planliu/HeadScanner/Solidworks_Files/SCANNER_outerarm_end.SLDPRT

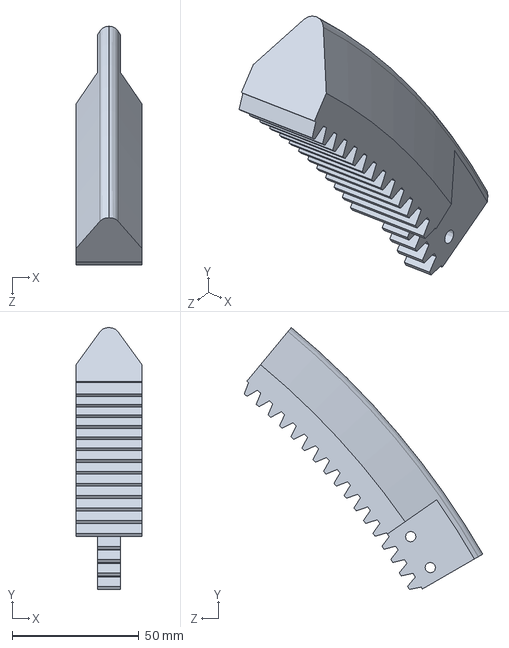
[picture p22: CAD file, 2024-10-23]
Solidworks_Files/SCANNER_outerarm_end.SLDPRT
26.0 x 103.2 x 94.0 mm
