planliu/HeadScanner/Solidworks_Files/SCANNER_uppergearlarge.SLDPRT

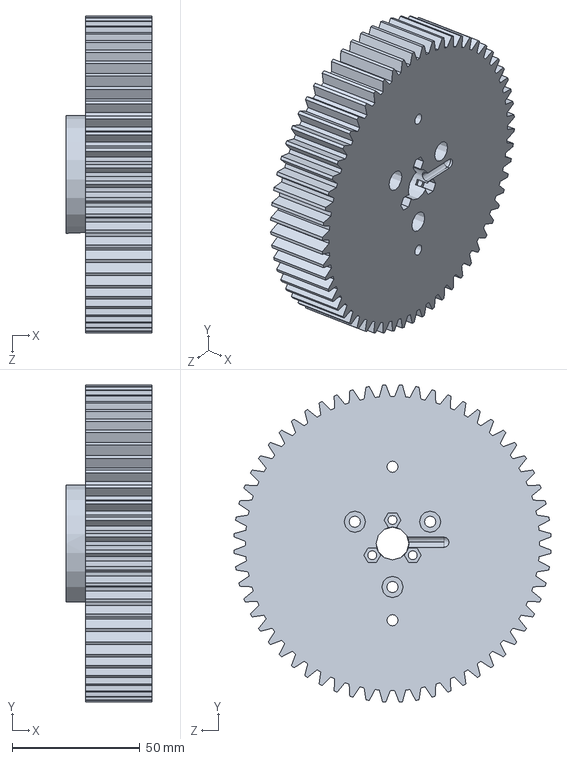
[picture p23: CAD file, 2024-10-23]
Solidworks_Files/SCANNER_uppergearlarge.SLDPRT
33.5 x 123.9 x 123.9 mm
