planliu/HeadScanner/Solidworks_Files/SCANNER_uppergearlargemating.SLDPRT

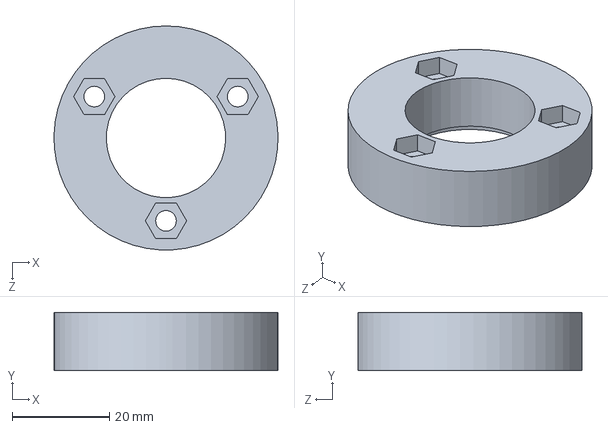
[picture p24: CAD file, 2024-10-23]
Solidworks_Files/SCANNER_uppergearlargemating.SLDPRT
46.0 x 12.0 x 46.0 mm
