planliu/HeadScanner/Solidworks_Files/SCANNER_shaft.SLDPRT

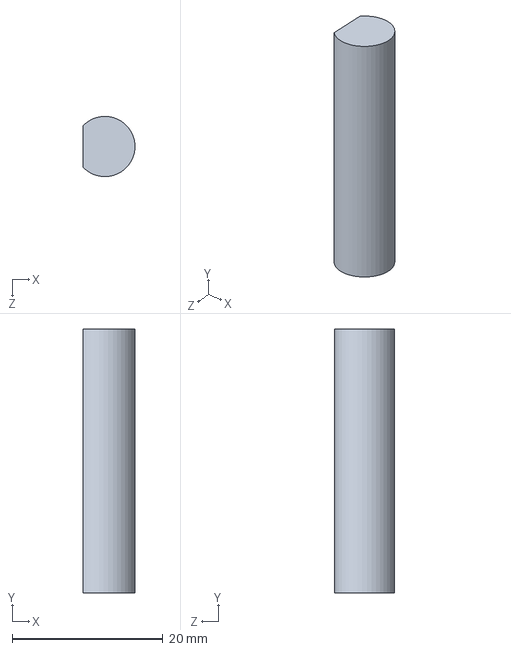
[picture p25: CAD file, 2024-10-23]
Solidworks_Files/SCANNER_shaft.SLDPRT
6.89 x 35.0 x 7.99 mm
