planliu/HeadScanner/Solidworks_Files/SCANNER_bodymidR.SLDPRT

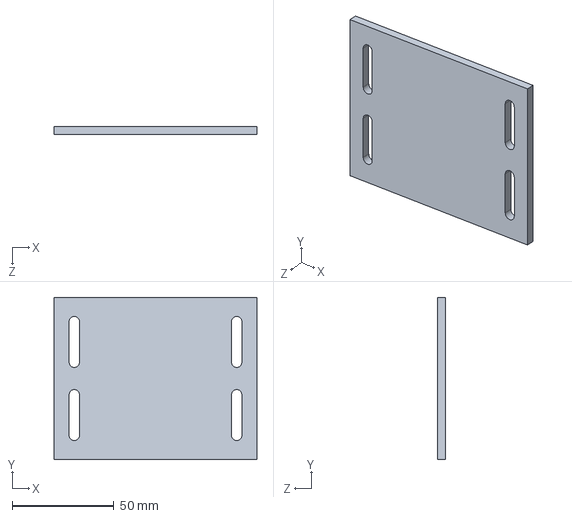
[picture p26: CAD file, 2024-10-23]
Solidworks_Files/SCANNER_bodymidR.SLDPRT
100.0 x 80.0 x 4.00 mm
