planliu/HeadScanner/Solidworks_Files/SCANNER_bodymidR2.SLDPRT

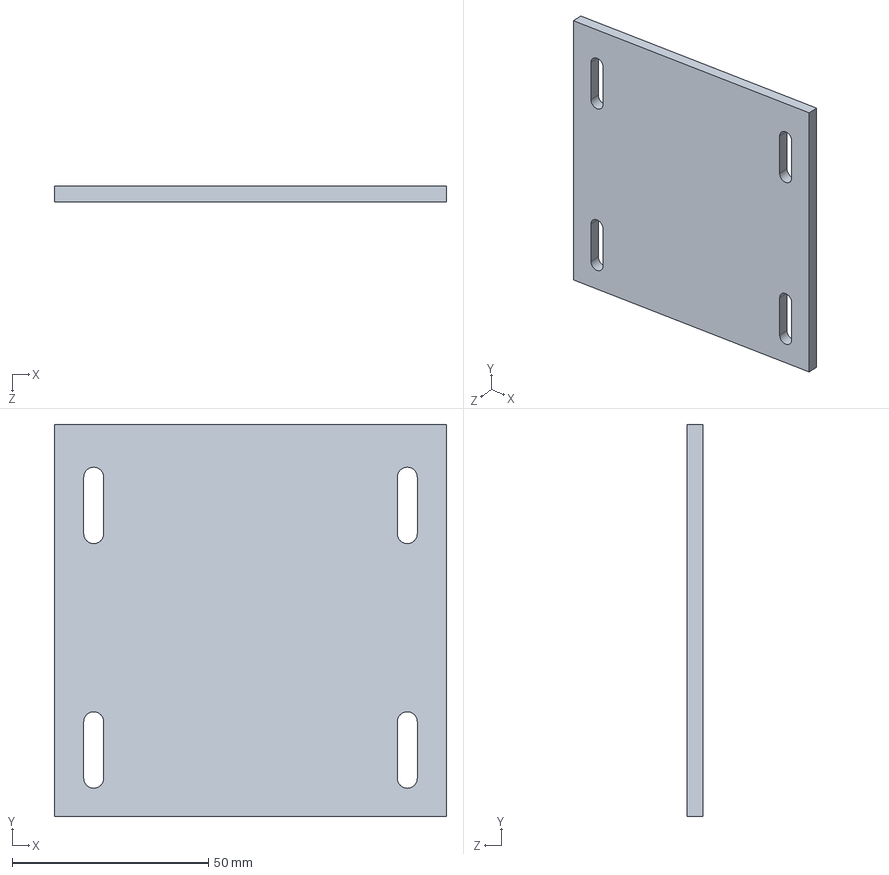
[picture p27: CAD file, 2024-10-23]
Solidworks_Files/SCANNER_bodymidR2.SLDPRT
100.0 x 100.0 x 4.00 mm
