planliu/HeadScanner/Solidworks_Files/SCANNER_innerarm_end.SLDPRT

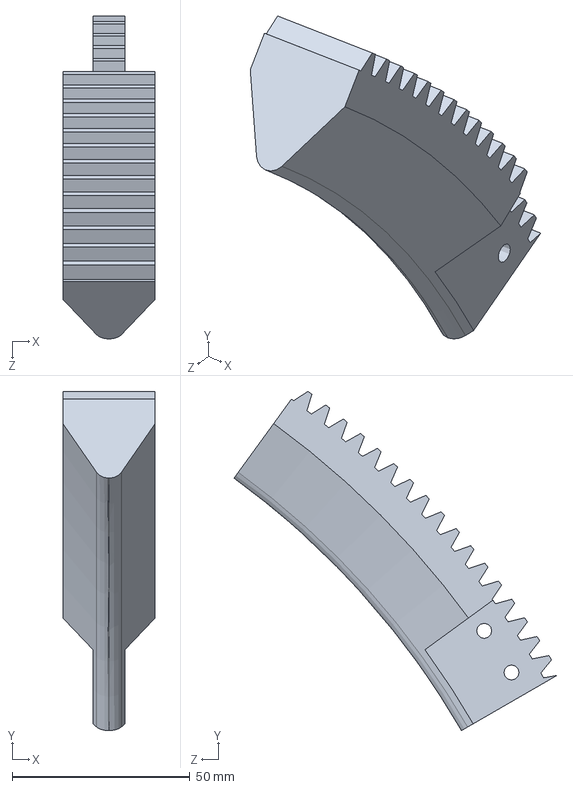
[picture p28: CAD file, 2024-10-23]
Solidworks_Files/SCANNER_innerarm_end.SLDPRT
26.0 x 95.5 x 90.9 mm
